nhicks00/camera-protective-cases/models/avkans_go_case/reports/avkans_go_preview.png

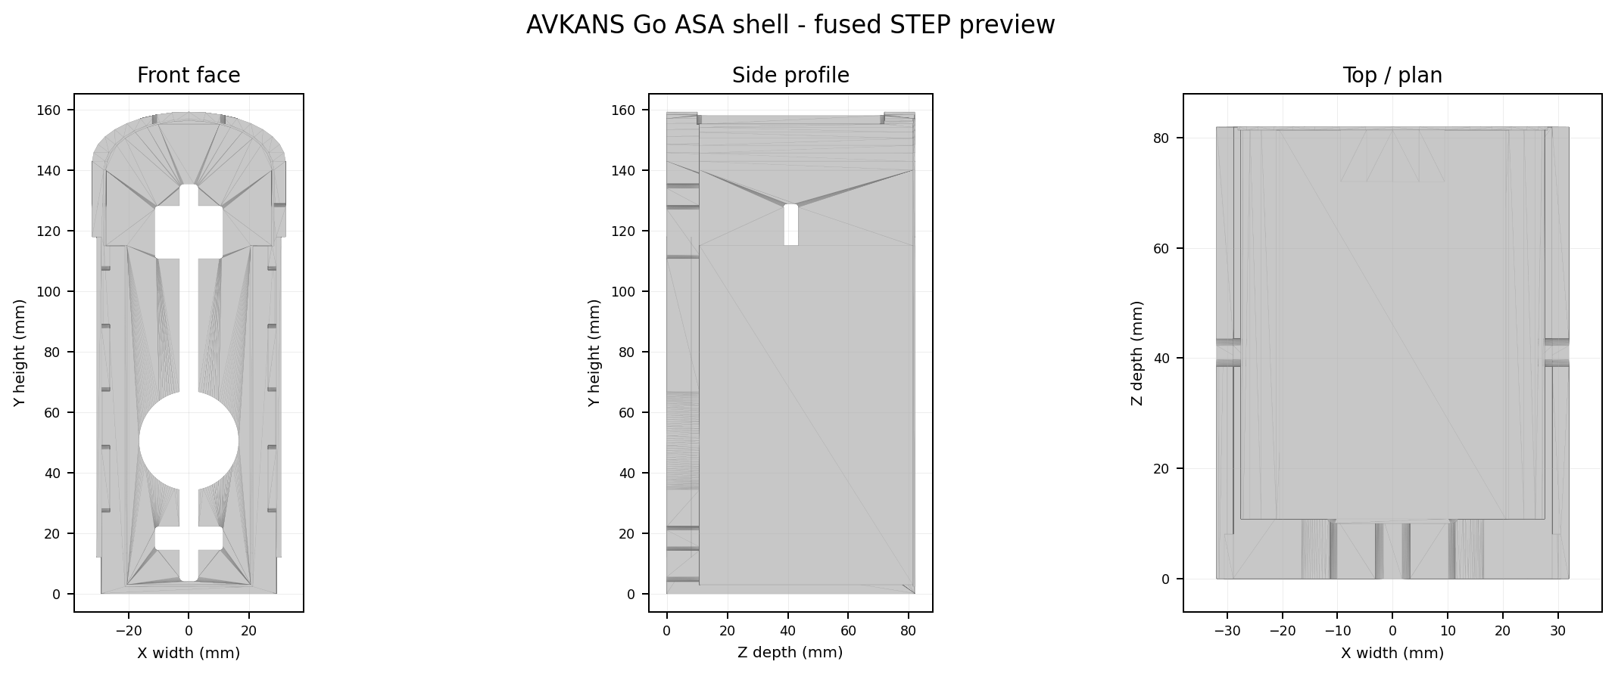
models/avkans_go_case/reports/avkans_go_preview.png
