nhicks00/camera-protective-cases/models/mevo_case/mevo_start_asa_shell.step

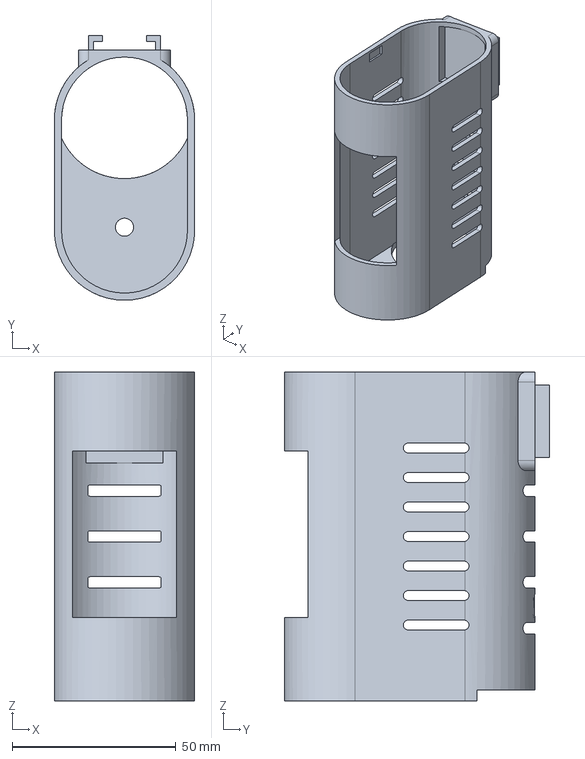
[picture p18: CAD file, 2026-03-08]
models/mevo_case/mevo_start_asa_shell.step
42.8 x 80.7 x 100.3 mm
