nhicks00/camera-protective-cases/models/zowietek_case/zowietek_pov_tpu_frame.stp

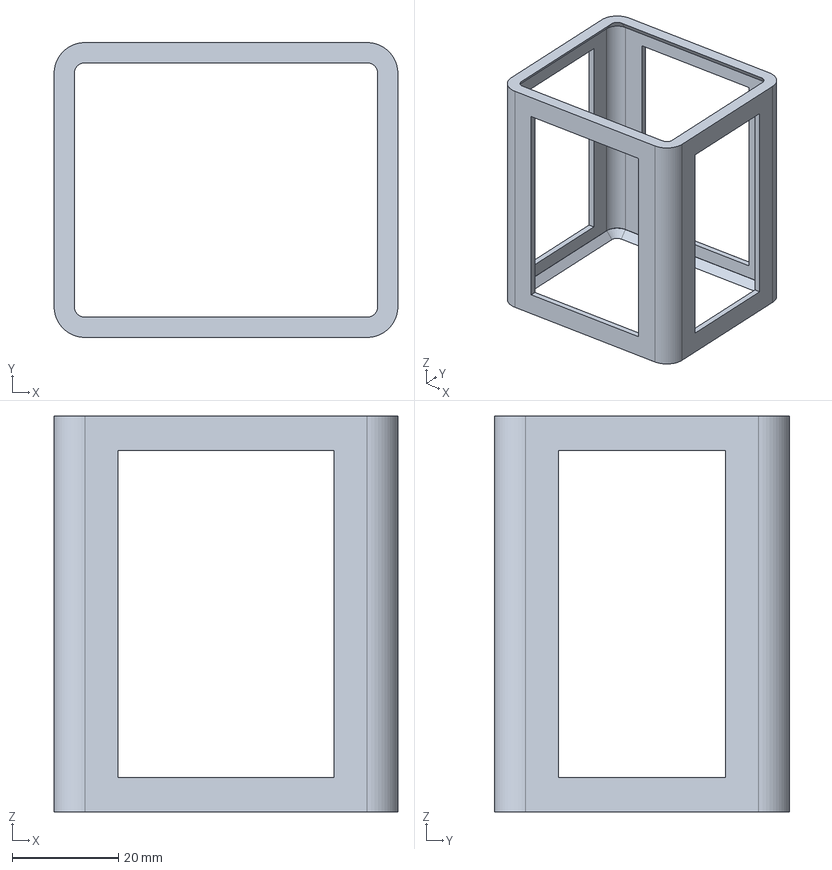
[picture p19: CAD file, 2026-03-19]
models/zowietek_case/zowietek_pov_tpu_frame.stp
64.6 x 55.4 x 74.4 mm
