nhicks00/camera-protective-cases/refs/mevo_lens_3.stl

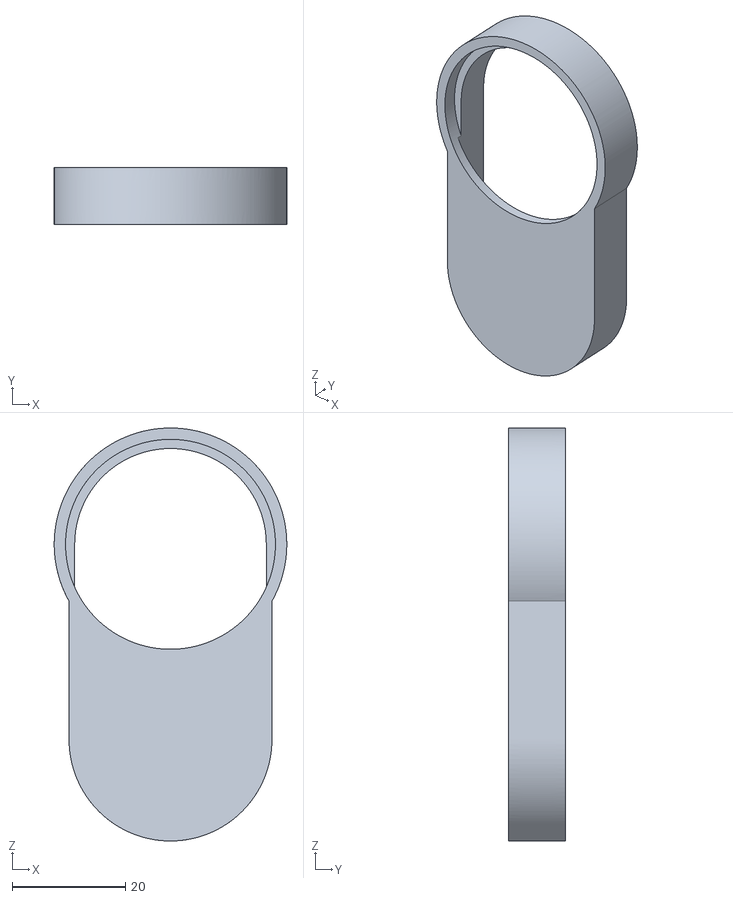
[picture p20: CAD file, 2026-03-02]
refs/mevo_lens_3.stl
41.0 x 10.0 x 72.8
