nhicks00/camera-protective-cases/models/mevo_case/mevo_start_body_dual_material.step

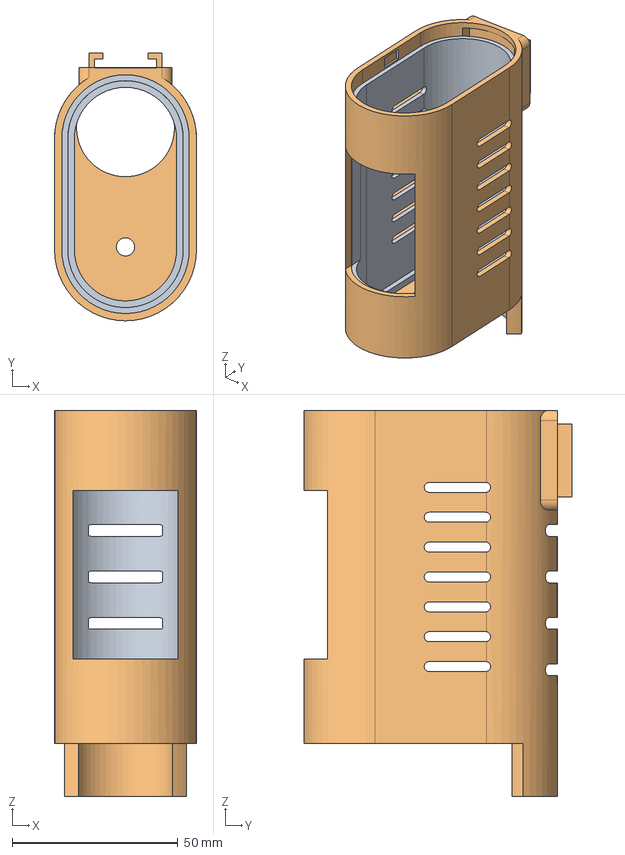
[picture p21: CAD file, 2026-03-06]
models/mevo_case/mevo_start_body_dual_material.step
42.8 x 80.7 x 116.3 mm
