nhicks00/camera-protective-cases/refs/Mevo_Start_lens_cover_corrected.stl

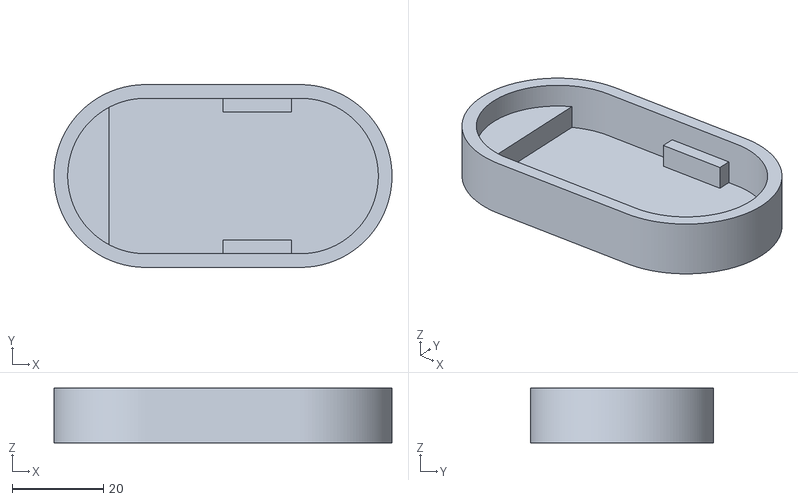
[picture p22: CAD file, 2026-03-02]
refs/Mevo_Start_lens_cover_corrected.stl
74.0 x 40.0 x 12.0
