nhicks00/camera-protective-cases/models/maki_case/maki_live_tpu_sleeve.step

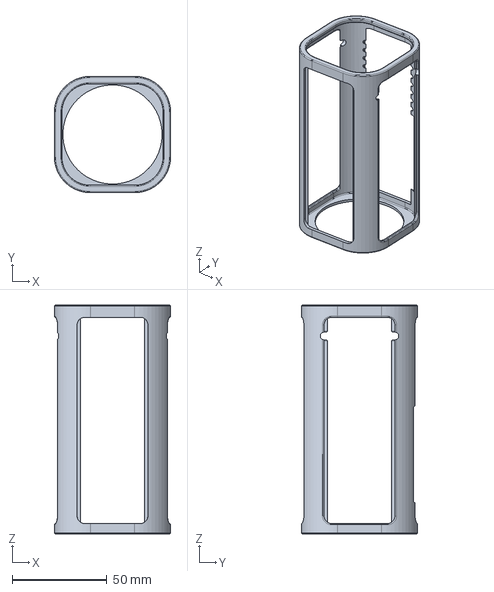
[picture p23: CAD file, 2026-03-21]
models/maki_case/maki_live_tpu_sleeve.step
61.3 x 61.3 x 120.7 mm
