nhicks00/camera-protective-cases/models/mevo_case/mevo_start_back_cap_dual_material.step

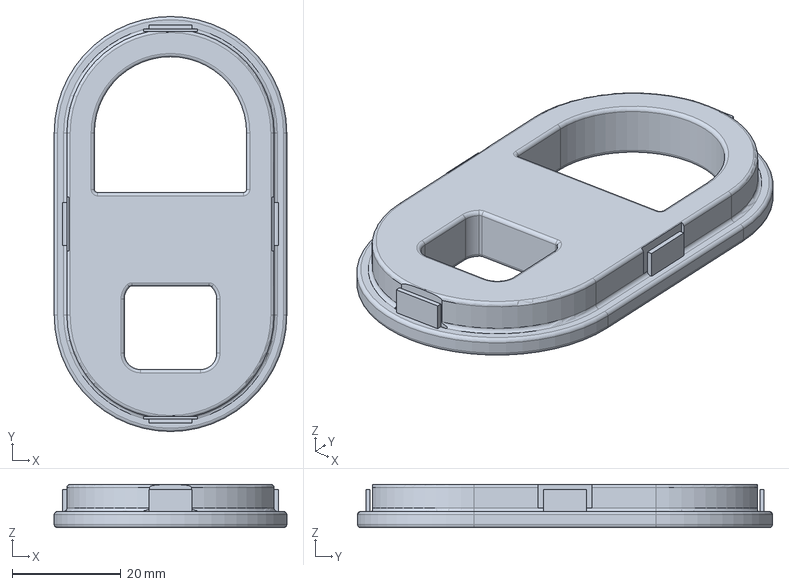
[picture p24: CAD file, 2026-03-06]
models/mevo_case/mevo_start_back_cap_dual_material.step
42.8 x 76.4 x 8.00 mm
