nhicks00/camera-protective-cases/models/maki_case/maki_live_rear_cap_dual_material.step

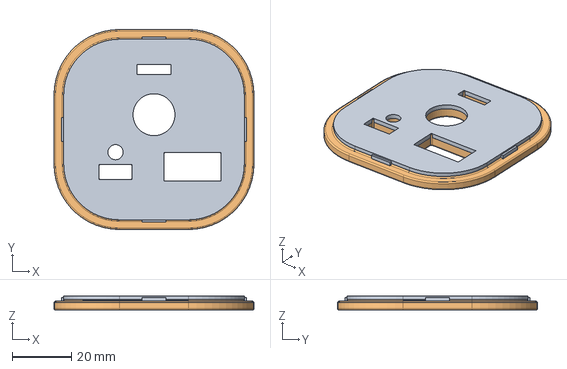
[picture p25: CAD file, 2026-03-08]
models/maki_case/maki_live_rear_cap_dual_material.step
67.6 x 67.6 x 4.80 mm
