nhicks00/camera-protective-cases/models/mevo_case/mevo_start_back_cap_asa.step

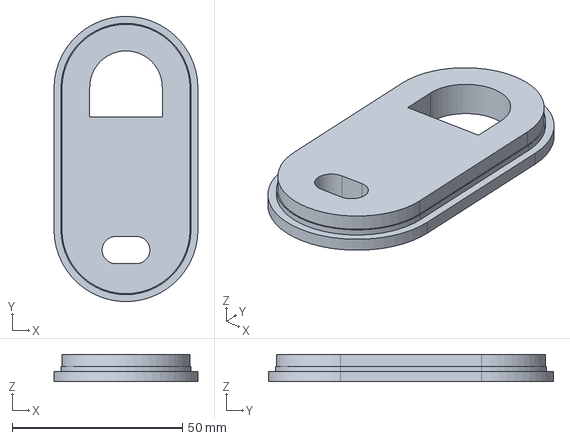
[picture p26: CAD file, 2026-03-02]
models/mevo_case/mevo_start_back_cap_asa.step
42.3 x 83.8 x 8.00 mm
