nhicks00/camera-protective-cases/models/maki_case/maki_live_body_dual_material.step

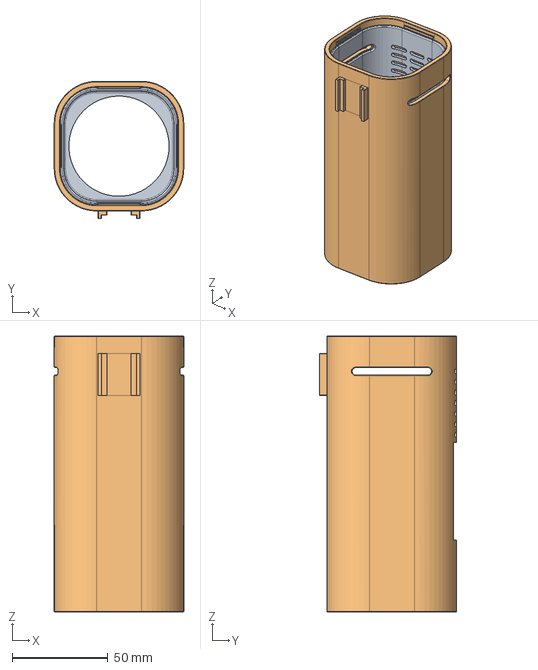
[picture p27: CAD file, 2026-03-05]
models/maki_case/maki_live_body_dual_material.step
67.6 x 71.6 x 143.9 mm
