nhicks00/camera-protective-cases/models/mevo_case/mevo_start_tpu_sleeve.step

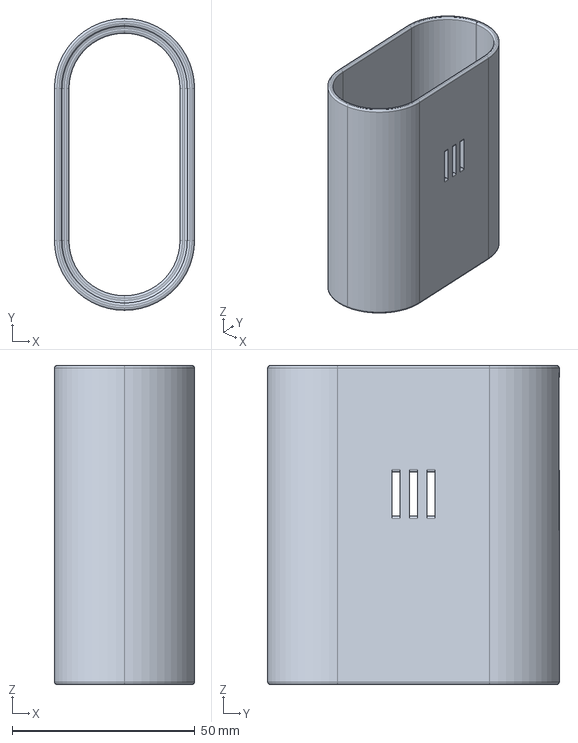
[picture p28: CAD file, 2026-03-02]
models/mevo_case/mevo_start_tpu_sleeve.step
38.4 x 79.9 x 87.4 mm
