nhicks00/camera-protective-cases/models/mevo_case/mevo_start_case_body.step

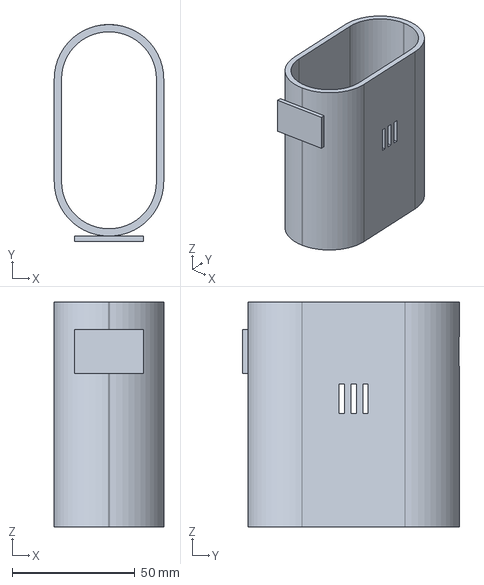
[picture p29: CAD file, 2026-03-02]
models/mevo_case/mevo_start_case_body.step
44.6 x 88.3 x 91.6 mm
