nhicks00/camera-protective-cases/models/mevo_case/mevo_start_rear_cap.step

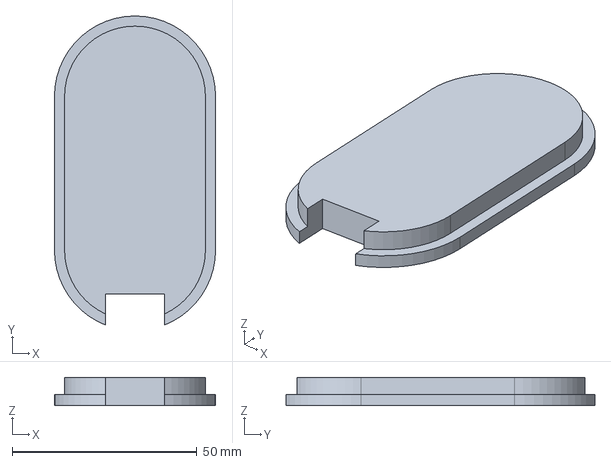
[picture p30: CAD file, 2026-03-02]
models/mevo_case/mevo_start_rear_cap.step
43.6 x 83.6 x 7.60 mm
