nhicks00/camera-protective-cases/models/maki_case/maki_live_tpu_unibody.step

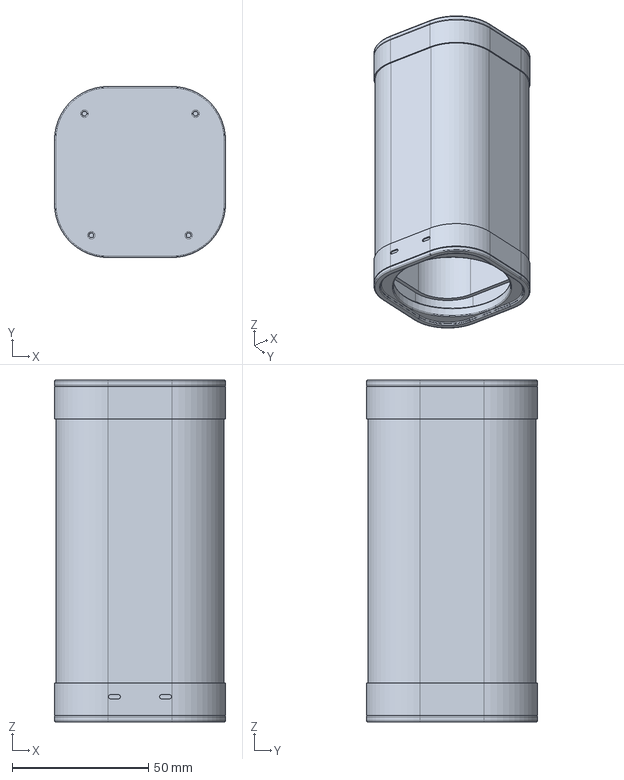
[picture p31: CAD file, 2026-03-02]
models/maki_case/maki_live_tpu_unibody.step
62.7 x 62.7 x 125.3 mm
