nhicks00/camera-protective-cases/models/mevo_case/mevo_start_front_cap.step

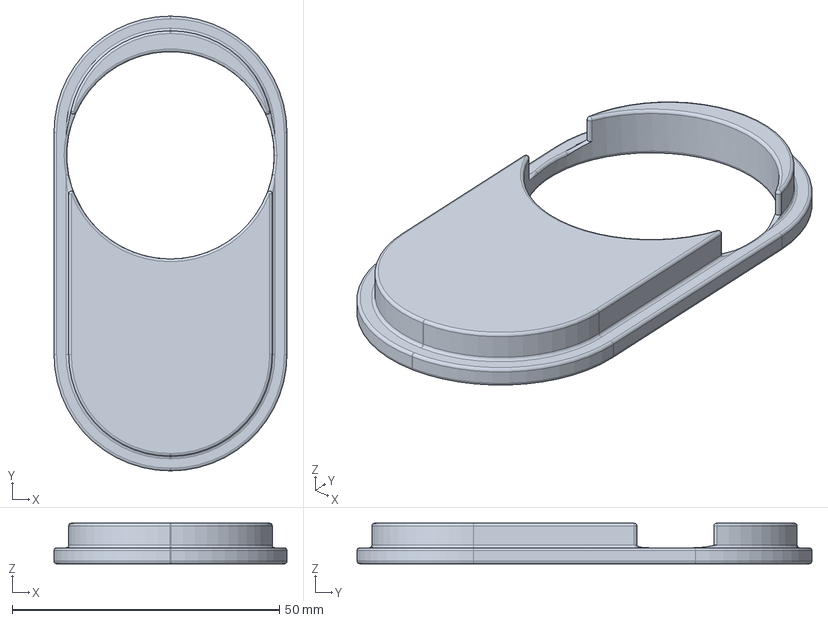
[picture p32: CAD file, 2026-03-02]
models/mevo_case/mevo_start_front_cap.step
43.6 x 85.1 x 7.60 mm
