nhicks00/camera-protective-cases/models/maki_case/maki_live_rear_cap.step

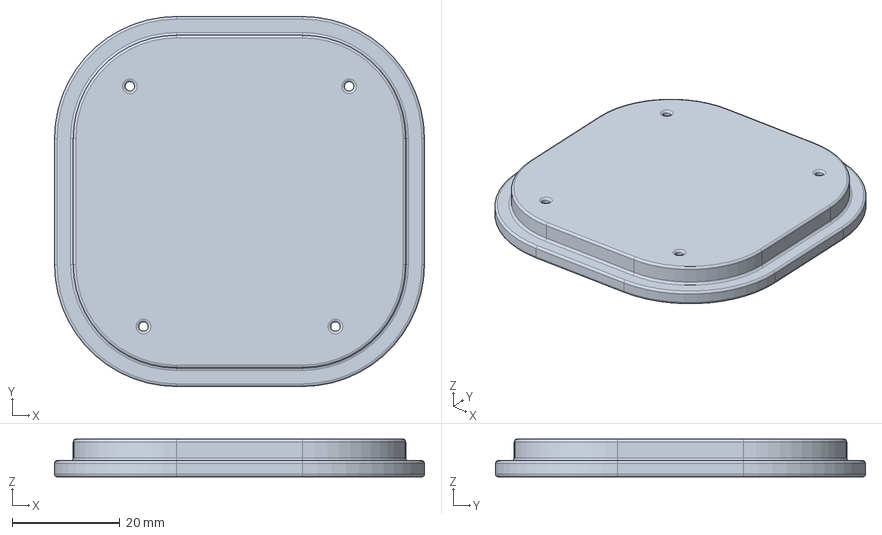
[picture p33: CAD file, 2026-03-02]
models/maki_case/maki_live_rear_cap.step
68.7 x 68.7 x 7.00 mm
