nhicks00/camera-protective-cases/models/mevo_case/mevo_start_tpu_liner.step

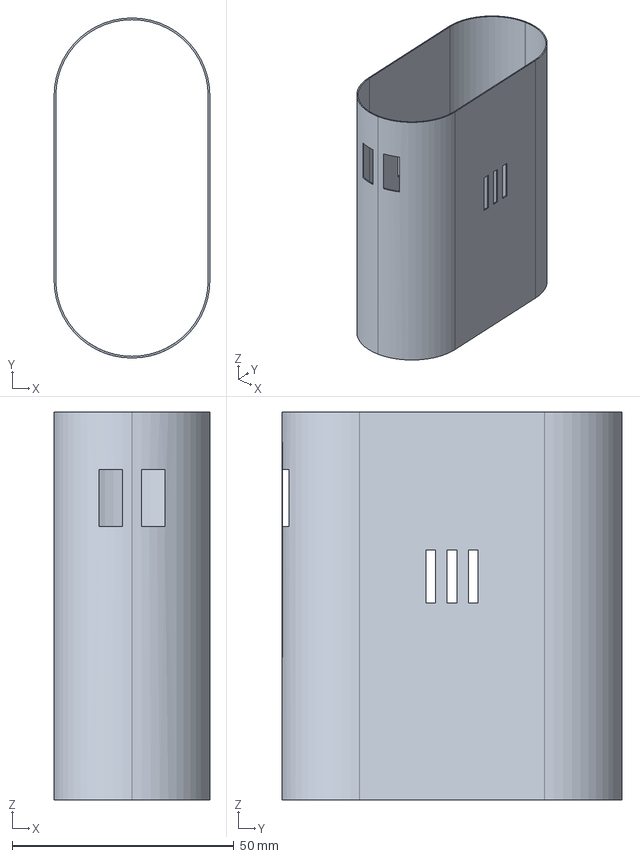
[picture p34: CAD file, 2026-03-02]
models/mevo_case/mevo_start_tpu_liner.step
35.1 x 76.6 x 87.4 mm
