nhicks00/camera-protective-cases/models/maki_case/maki_live_front_cap.step

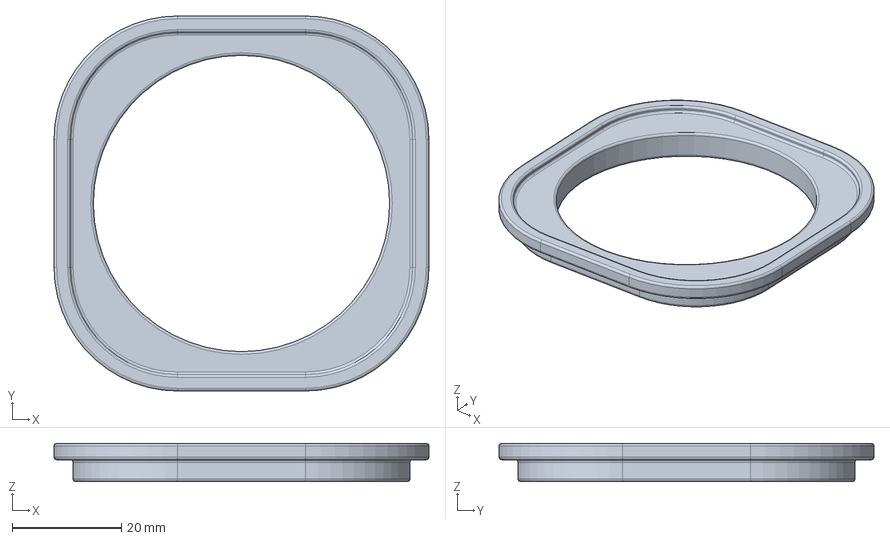
[picture p35: CAD file, 2026-03-02]
models/maki_case/maki_live_front_cap.step
68.7 x 68.7 x 7.00 mm
