nhicks00/camera-protective-cases/models/mevo_case/mevo_start_tpu_rear_cap.step

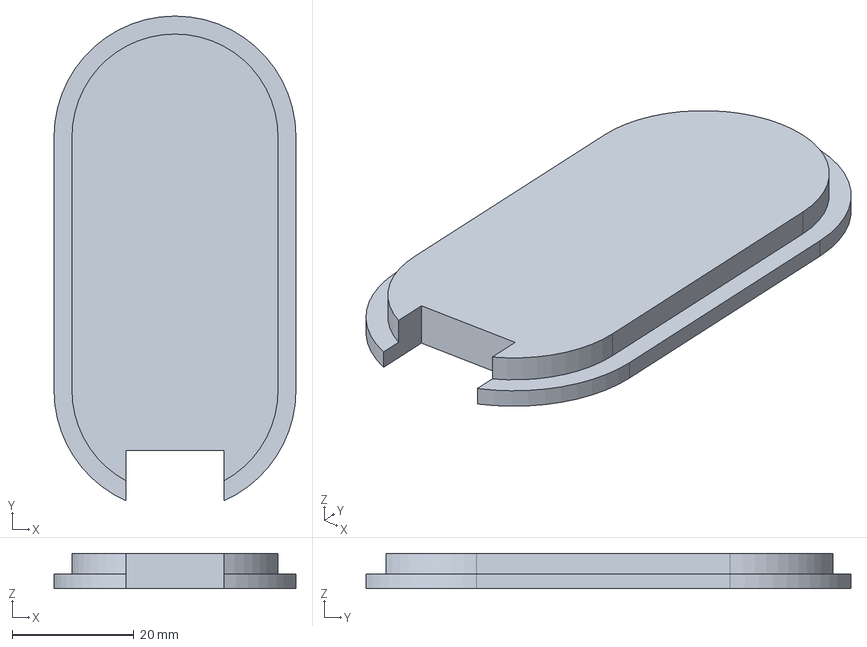
[picture p36: CAD file, 2026-03-02]
models/mevo_case/mevo_start_tpu_rear_cap.step
39.7 x 79.5 x 5.80 mm
