nhicks00/camera-protective-cases/models/maki_case/maki_live_tpu_front_cap.step

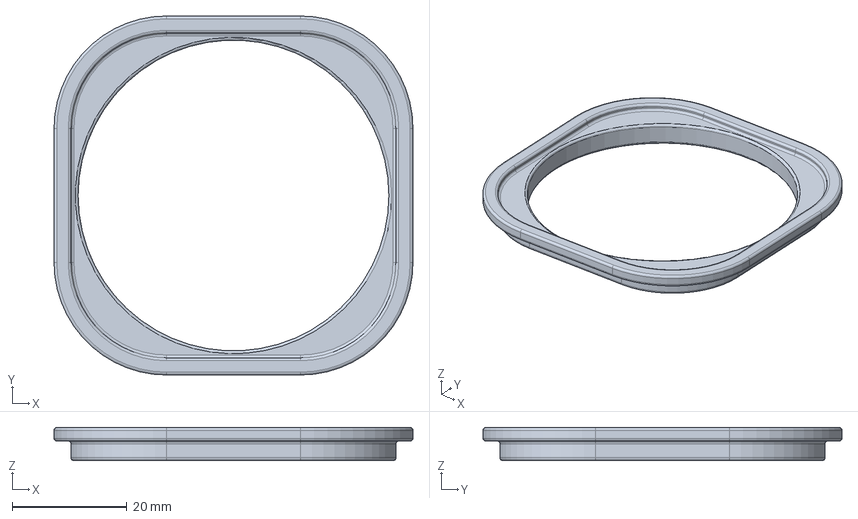
[picture p37: CAD file, 2026-03-02]
models/maki_case/maki_live_tpu_front_cap.step
62.7 x 62.7 x 5.80 mm
