nhicks00/camera-protective-cases/models/mevo_case/mevo_start_tpu_front_cap.step

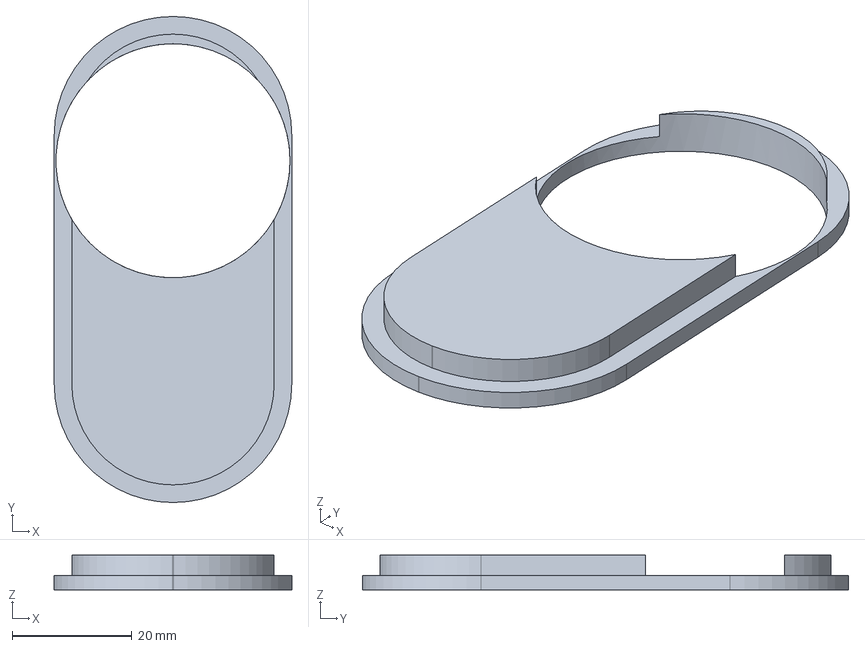
[picture p38: CAD file, 2026-03-02]
models/mevo_case/mevo_start_tpu_front_cap.step
39.7 x 81.2 x 5.80 mm
