nhicks00/camera-protective-cases/models/mevo_case/mevo_start_case_back_plate.step

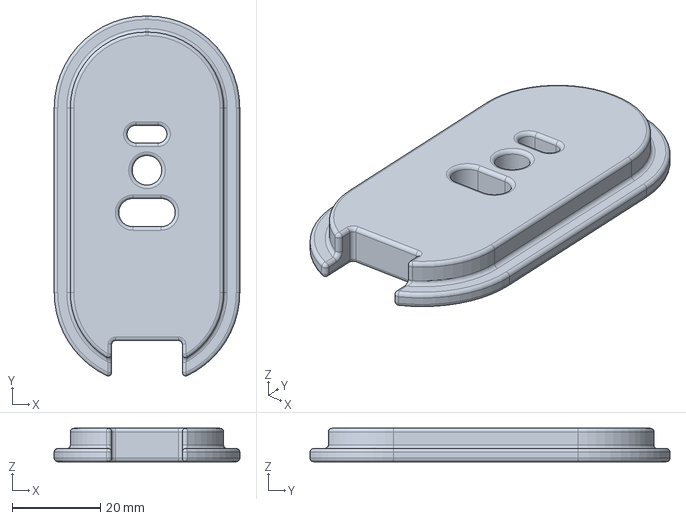
[picture p40: CAD file, 2026-03-02]
models/mevo_case/mevo_start_case_back_plate.step
42.1 x 81.7 x 7.60 mm
