nhicks00/camera-protective-cases/models/maki_case/maki_live_tpu_liner.step

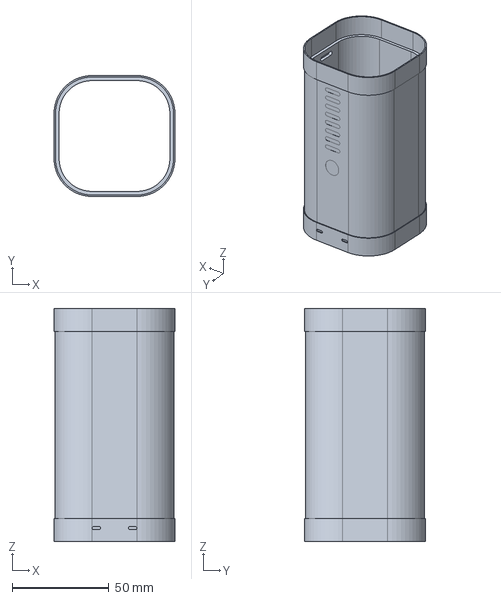
[picture p41: CAD file, 2026-03-02]
models/maki_case/maki_live_tpu_liner.step
62.7 x 62.7 x 120.7 mm
